NickStassen/nicklink/sim/results/ldo_steps.png

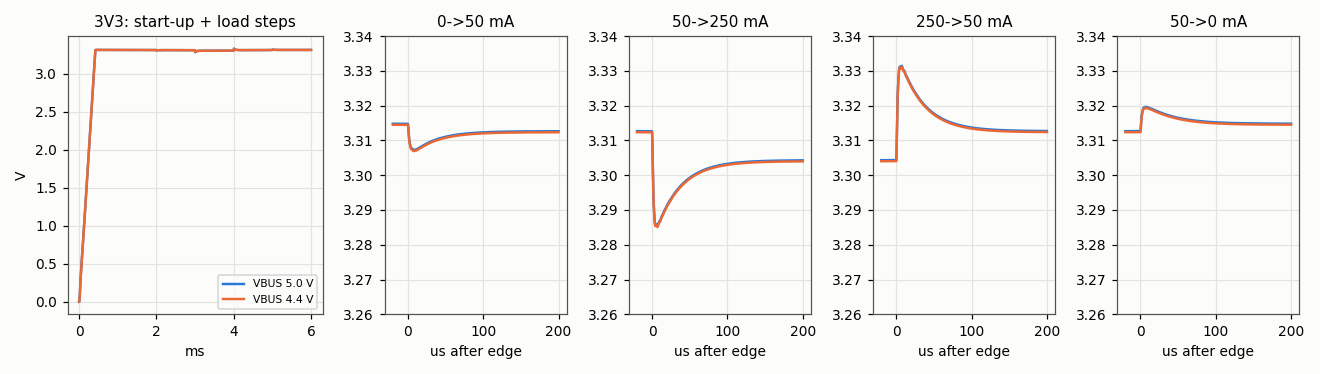
sim/results/ldo_steps.png
