NickStassen/nicklink/sim/results/brownout.png

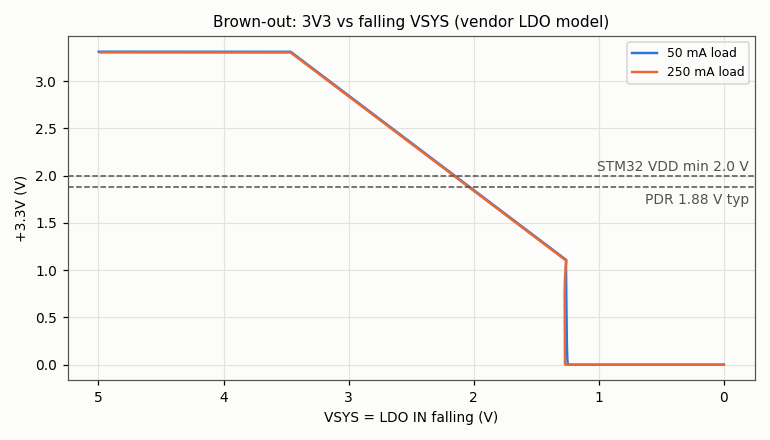
sim/results/brownout.png
