NickStassen/nicklink/sim/results/hotplug_base.png

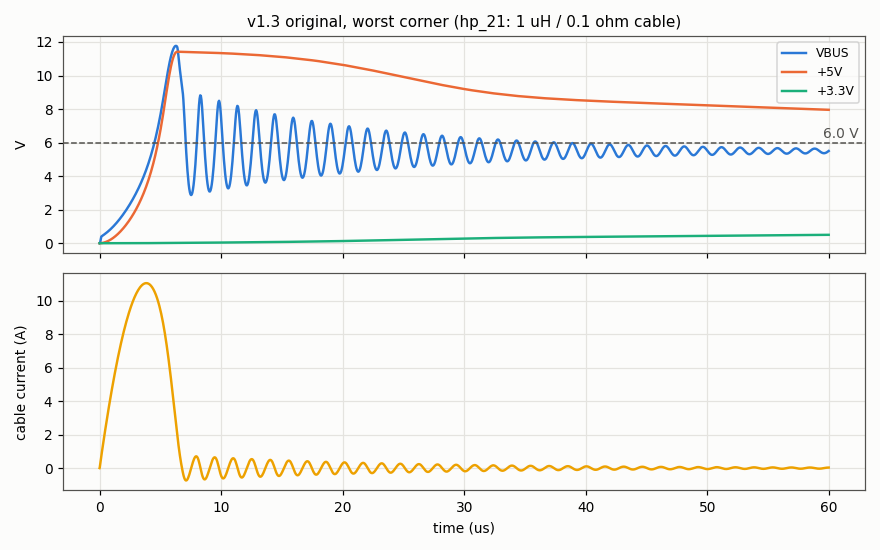
sim/results/hotplug_base.png
