NickStassen/nicklink/sim/results/hotplug_variants.png

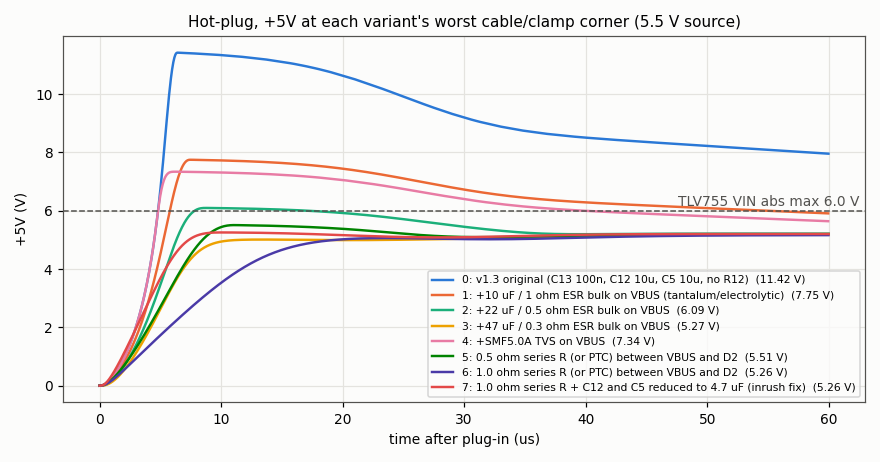
sim/results/hotplug_variants.png
