NickStassen/nicklink/sim/results/i2c.png

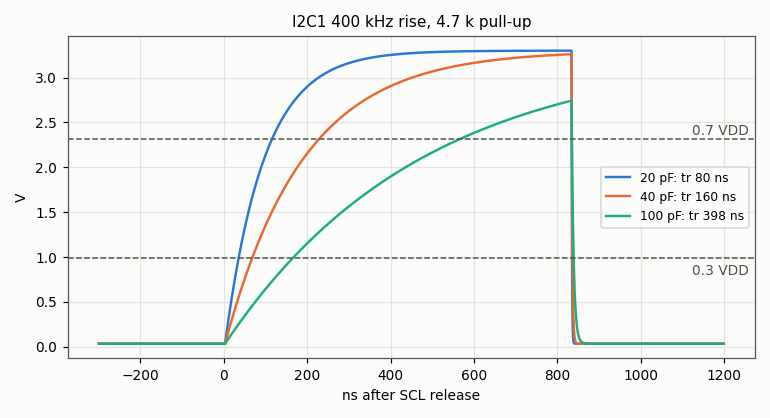
sim/results/i2c.png
