NickStassen/nicklink/sim/results/led_r6.png

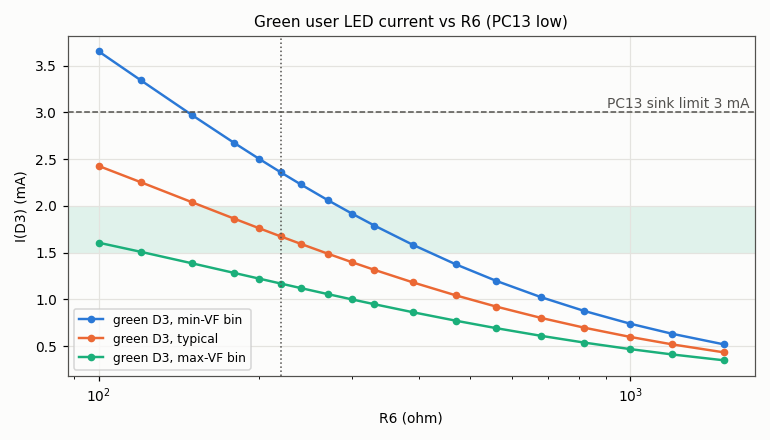
sim/results/led_r6.png
