NickStassen/nicklink/sim/results/nrst.png

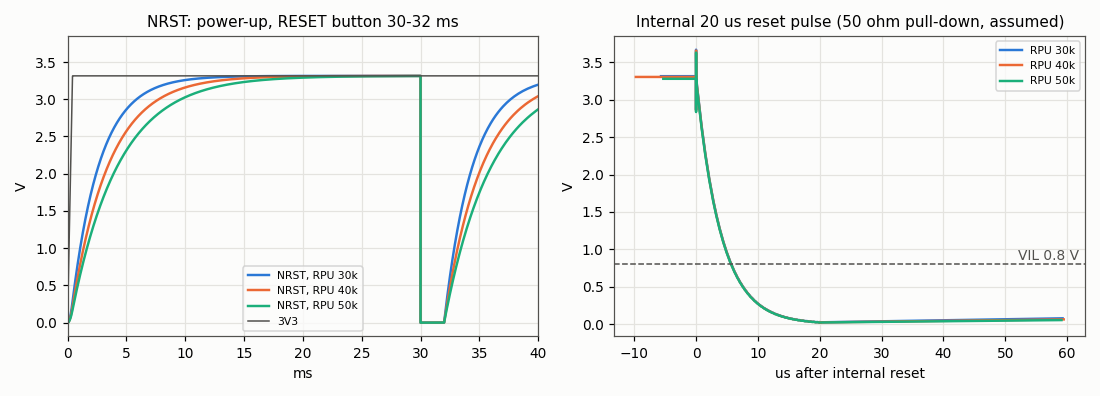
sim/results/nrst.png
