NickStassen/nicklink/sim/results/snubber.png

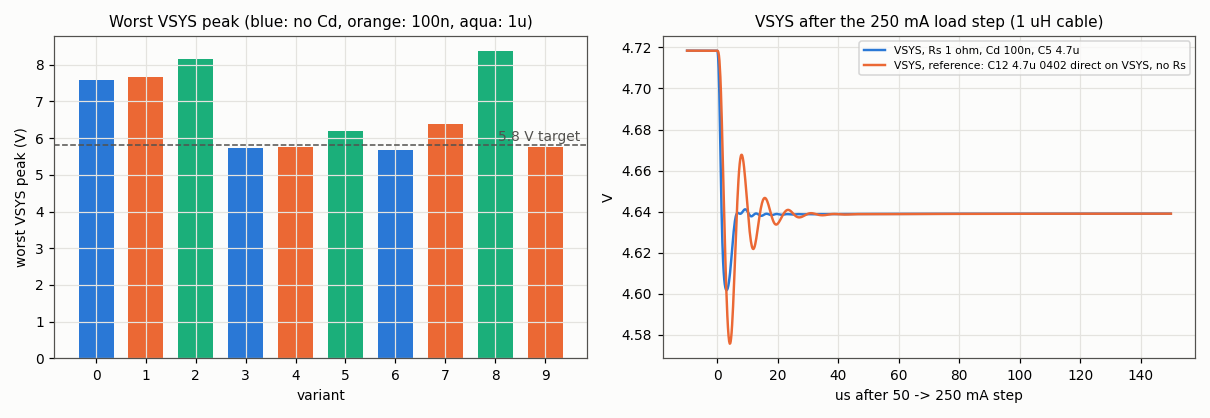
sim/results/snubber.png
