NickStassen/nicklink/sim/results/vdda.png

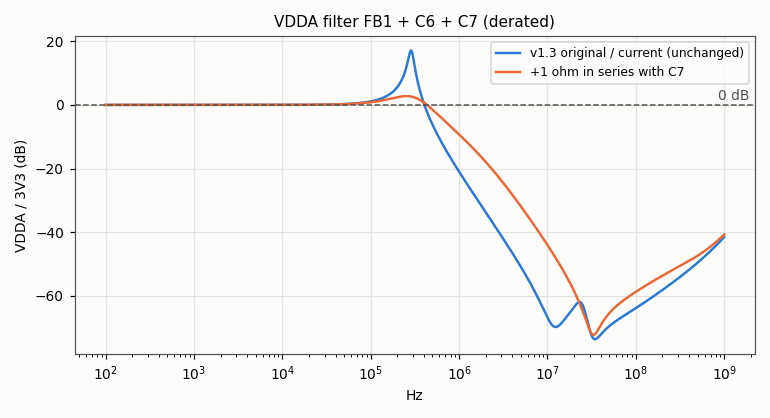
sim/results/vdda.png
