NickStassen/nicklink/sim/results/hotplug_fixes.png

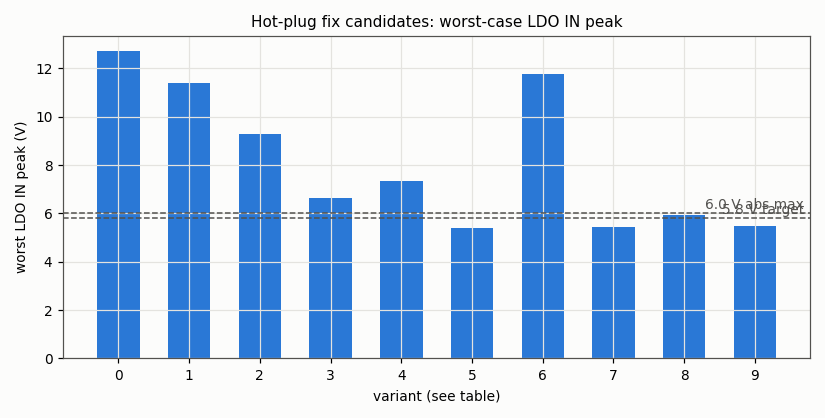
sim/results/hotplug_fixes.png
